Jason2062/2D-Printer/PrinterGUI/ui_widget.h

/********************************************************************************
** Form generated from reading UI file 'widget.ui'
**
** Created by: Qt User Interface Compiler version 5.7.1
**
** WARNING! All changes made in this file will be lost when recompiling UI file!
********************************************************************************/

#ifndef UI_WIDGET_H
#define UI_WIDGET_H

#include <QtCore/QVariant>
#include <QtWidgets/QAction>
#include <QtWidgets/QApplication>
#include <QtWidgets/QButtonGroup>
#include <QtWidgets/QFormLayout>
#include <QtWidgets/QHBoxLayout>
#include <QtWidgets/QHeaderView>
#include <QtWidgets/QLabel>
#include <QtWidgets/QLineEdit>
#include <QtWidgets/QPushButton>
#include <QtWidgets/QSpacerItem>
#include <QtWidgets/QSpinBox>
#include <QtWidgets/QVBoxLayout>
#include <QtWidgets/QWidget>

QT_BEGIN_NAMESPACE

class Ui_Widget
{
public:
    QVBoxLayout *verticalLayout_4;
    QVBoxLayout *verticalLayout_3;
    QPushButton *pushButton;
    QHBoxLayout *horizontalLayout_2;
    QLabel *label;
    QLineEdit *estadoLineEdit;
    QHBoxLayout *horizontalLayout;
    QVBoxLayout *verticalLayout;
    QLabel *label_2;
    QSpacerItem *verticalSpacer;
    QVBoxLayout *verticalLayout_2;
    QFormLayout *formLayout;
    QLabel *label_3;
    QSpinBox *xPosSpinBox;
    QFormLayout *formLayout_2;
    QLabel *label_4;
    QSpinBox *yPosSpinBox;
    QSpacerItem *verticalSpacer_3;
    QSpacerItem *verticalSpacer_2;

    void setupUi(QWidget *Widget)
    {
        if (Widget->objectName().isEmpty())
            Widget->setObjectName(QStringLiteral("Widget"));
        Widget->resize(1016, 576);
        verticalLayout_4 = new QVBoxLayout(Widget);
        verticalLayout_4->setSpacing(6);
        verticalLayout_4->setContentsMargins(11, 11, 11, 11);
        verticalLayout_4->setObjectName(QStringLiteral("verticalLayout_4"));
        verticalLayout_3 = new QVBoxLayout();
        verticalLayout_3->setSpacing(6);
        verticalLayout_3->setObjectName(QStringLiteral("verticalLayout_3"));
        pushButton = new QPushButton(Widget);
        pushButton->setObjectName(QStringLiteral("pushButton"));

        verticalLayout_3->addWidget(pushButton);

        horizontalLayout_2 = new QHBoxLayout();
        horizontalLayout_2->setSpacing(6);
        horizontalLayout_2->setObjectName(QStringLiteral("horizontalLayout_2"));
        label = new QLabel(Widget);
        label->setObjectName(QStringLiteral("label"));

        horizontalLayout_2->addWidget(label);

        estadoLineEdit = new QLineEdit(Widget);
        estadoLineEdit->setObjectName(QStringLiteral("estadoLineEdit"));

        horizontalLayout_2->addWidget(estadoLineEdit);


        verticalLayout_3->addLayout(horizontalLayout_2);

        horizontalLayout = new QHBoxLayout();
        horizontalLayout->setSpacing(6);
        horizontalLayout->setObjectName(QStringLiteral("horizontalLayout"));
        verticalLayout = new QVBoxLayout();
        verticalLayout->setSpacing(6);
        verticalLayout->setObjectName(QStringLiteral("verticalLayout"));
        label_2 = new QLabel(Widget);
        label_2->setObjectName(QStringLiteral("label_2"));

        verticalLayout->addWidget(label_2);

        verticalSpacer = new QSpacerItem(20, 40, QSizePolicy::Minimum, QSizePolicy::Expanding);

        verticalLayout->addItem(verticalSpacer);


        horizontalLayout->addLayout(verticalLayout);

        verticalLayout_2 = new QVBoxLayout();
        verticalLayout_2->setSpacing(6);
        verticalLayout_2->setObjectName(QStringLiteral("verticalLayout_2"));
        formLayout = new QFormLayout();
        formLayout->setSpacing(6);
        formLayout->setObjectName(QStringLiteral("formLayout"));
        label_3 = new QLabel(Widget);
        label_3->setObjectName(QStringLiteral("label_3"));

        formLayout->setWidget(0, QFormLayout::LabelRole, label_3);

        xPosSpinBox = new QSpinBox(Widget);
        xPosSpinBox->setObjectName(QStringLiteral("xPosSpinBox"));

        formLayout->setWidget(0, QFormLayout::FieldRole, xPosSpinBox);


        verticalLayout_2->addLayout(formLayout);

        formLayout_2 = new QFormLayout();
        formLayout_2->setSpacing(6);
        formLayout_2->setObjectName(QStringLiteral("formLayout_2"));
        label_4 = new QLabel(Widget);
        label_4->setObjectName(QStringLiteral("label_4"));

        formLayout_2->setWidget(0, QFormLayout::LabelRole, label_4);

        yPosSpinBox = new QSpinBox(Widget);
        yPosSpinBox->setObjectName(QStringLiteral("yPosSpinBox"));

        formLayout_2->setWidget(0, QFormLayout::FieldRole, yPosSpinBox);

        verticalSpacer_3 = new QSpacerItem(20, 40, QSizePolicy::Minimum, QSizePolicy::Expanding);

        formLayout_2->setItem(1, QFormLayout::FieldRole, verticalSpacer_3);


        verticalLayout_2->addLayout(formLayout_2);


        horizontalLayout->addLayout(verticalLayout_2);


        verticalLayout_3->addLayout(horizontalLayout);


        verticalLayout_4->addLayout(verticalLayout_3);

        verticalSpacer_2 = new QSpacerItem(20, 108, QSizePolicy::Minimum, QSizePolicy::Expanding);

        verticalLayout_4->addItem(verticalSpacer_2);


        retranslateUi(Widget);

        QMetaObject::connectSlotsByName(Widget);
    } // setupUi

    void retranslateUi(QWidget *Widget)
    {
        Widget->setWindowTitle(QApplication::translate("Widget", "Widget", Q_NULLPTR));
        pushButton->setText(QApplication::translate("Widget", "PushButton", Q_NULLPTR));
        label->setText(QApplication::translate("Widget", "Estado", Q_NULLPTR));
        label_2->setText(QApplication::translate("Widget", "Posicion", Q_NULLPTR));
        label_3->setText(QApplication::translate("Widget", "X", Q_NULLPTR));
        label_4->setText(QApplication::translate("Widget", "Y", Q_NULLPTR));
    } // retranslateUi

};

namespace Ui {
    class Widget: public Ui_Widget {};
} // namespace Ui

QT_END_NAMESPACE

#endif // UI_WIDGET_H
