Jason2062/2D-Printer/PrinterGUI/qtglobal.cpp

#include "qtglobal.h"

qtGlobal::qtGlobal()
{

}

qtGlobal::~qtGlobal()
{

}

//store coordinate (x,y)
/**
 * @brief qtGlobal::xValue initialize the xValue
 */
int qtGlobal::xValue=0;
/**
 * @brief qtGlobal::yValue initialize the xValue
 */
int qtGlobal::yValue=0;

bool qtGlobal::servoState=true;
